pierreca/LightClock/LoopHelpers.h

#pragma once

char incrementOrLoop(char current, char max, char min = '0');
char decrementOrLoop(char current, char max, char min = '0');
int incrementOrLoop(int current, int max, int min = 0);
int decrementOrLoop(int current, int max, int min = 0);
